techlabtl/KitMonitorScuola/v1-2015/Tutorial/Configurazione/test_sensori/test_sensori.ino

#include <DHT.h>
#include <EmonLib.h>                   // Include Emon Library

EnergyMonitor emon1;                   // Create an instance

#define DHT_PIN A3 // what pin we're connected to
#define CT_PIN A4
#define LIGHT_PIN A2
#define SOUND_PIN A1
#define AIR_PIN A0

#define DHTTYPE DHT22 // DHT 22 (AM2302)
DHT dht(DHT_PIN, DHTTYPE);

long int j =   0;
int jj = 0;

void setup()
{
  emon1.current(CT_PIN, 98.77);
  dht.begin();
  Serial.begin(9600);
}

void loop()
{
  
  String dataString;
  //QUALITA' ARIA
  dataString += "QUALITA' ARIA: ";
  dataString += analogRead(AIR_PIN);
  dataString += '\n';
  

  //LUMINOSITA'
  dataString += "LUMINOSITA': ";
  dataString += analogRead(LIGHT_PIN);
  dataString += '\n';

  //RUMORE
  dataString += "PRESSIONE SONORA': ";
  for (int i = 0; i < 3000; i++) {
    j += analogRead(SOUND_PIN);
  }
  dataString += j / 3000;
  dataString += '\n';

  j = 0;

  //UMIDITA'
  dataString += "UMIDITA': ";
  float h = dht.readHumidity();
  dataString += h;
  dataString += '\n';

  //TEMPERATURA
  dataString += "TEMPERATURA: ";
  float t = dht.readTemperature() - 4; //correzione temperatura
  dataString += t;
  dataString += '\n';

  //CORRENTE
  dataString += "CORRENTE: ";
  double Irms = emon1.calcIrms(1480);  // Calculate Irms only
  Irms -= 0.5;

  Serial.println(dataString);

  //Fai un lampeggio del led rosso quando ha finito di leggere tutti i dati
  digitalWrite(13, HIGH);
  delay(300);
  digitalWrite(13, LOW);

}
